matthewcieplak/super-sixteen/graphics/glide-graph.png

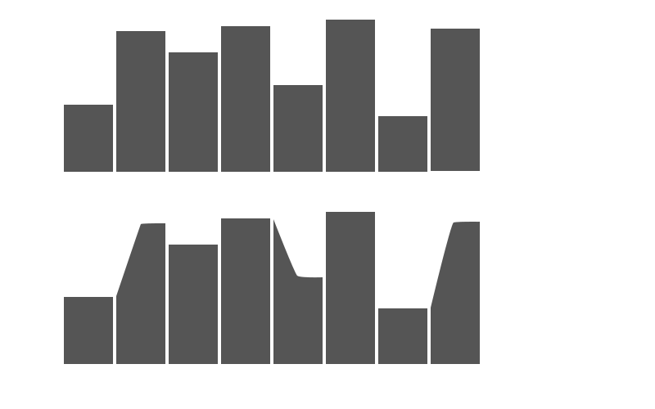
graphics/glide-graph.png
