matthewcieplak/super-sixteen/graphics/calibrate_screen.png

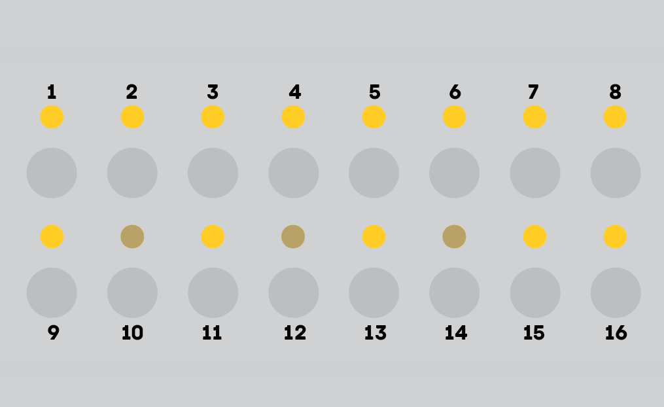
graphics/calibrate_screen.png
