matthewcieplak/super-sixteen/sequencer_app_v2/src/LEDMatrix.cpp

#include <Arduino.h>
#include "Variables.h"
#include "Pinout.h"
#include "Display.h"
#include "Sequencer.h"
#include "LEDMatrix.h"
#include "Buttons.h"
#include "Font.h"

namespace supersixteen{

elapsedMillis multiplex;
elapsedMillis blinker;
bool led_matrix[17];
int step_map[17] = { 3, 2, 1, 0, 0, 1, 2 ,3, 3, 2, 1, 0, 0, 1, 2, 3, 0 }; //rows are wired symmetrically rather than sequentially
int selected_step_led = 0;
const int MILLISECONDS_PER_MULTIPLEX = 1;
const int MILLISECONDS_AFTER_MULTIPLEX = 0;
bool display_active = 1;
byte visible_bar = 0;

uint8_t byte1;
uint8_t byte2;

int row_counter = 0;
int col = 0;
int j;

byte dataToSend;

Display* displayVar3;	
Sequencer* sequencerVar3;

void LedMatrix::init(Display& display, Sequencer& sequencer) {
	pinMode(CS1_PIN, OUTPUT);
	SPI.begin();
	displayVar3 = &display;
	sequencerVar3 = &sequencer;
}

void LedMatrix::updateMatrix(int row) {
	byte1 = (1 << (7-row)); //turn on row driver
	byte2 = 0xF0;
	for (col = 0; col < 4; col++) {
		byte2 +=  (led_matrix[row * 4 + col] << step_map[row * 4 + col]);
	}
	byte1 += ~byte2;
	PORTB = ~_BV(1) & PORTB; //equivalent to digitalWrite(CS1_PIN, LOW);
	SPI.setBitOrder(LSBFIRST); //shift registers like LSB
	displayVar3->updateSevenSegmentDisplay(); //has to happen HERE bc it's part of the shift register 2-byte sequence
	SPI.transfer(byte1); //led matrix  - NOTE: invert this byte if you've wired the LEDs backwards
	PORTB = _BV(1) | PORTB; //equivalent to digitalWrite(CS1_PIN, HIGH);
	displayVar3->nextDigit();
}

void LedMatrix::blankMatrix(int row) {
	displayVar3->blankSevenSegmentDisplay();
	return; //avoid flicker in matrix
	
	byte1 = (1 << (7-row)); //turn on row driver
	byte2 = 0xF0;
	byte1 += ~byte2;
	//PORTB = PORTB & B10111111; //equivalent to 
	digitalWrite(CS1_PIN, LOW);
	SPI.setBitOrder(LSBFIRST); //shift registers like LSB
	displayVar3->blankSevenSegmentDisplay(); //has to happen HERE bc it's part of the shift register 2-byte sequence
	SPI.transfer(~byte1); //led matrix
	//PORTB = PORTB | B01000000; //equivalent to 
	digitalWrite(CS1_PIN, HIGH);
	//displayVar3->nextDigit();
}

void LedMatrix::multiplexLeds() {
	//if (!display_active) {
	  if (multiplex > MILLISECONDS_AFTER_MULTIPLEX) {
	 	multiplex = 0;

		updateMatrix(row_counter);
		//readButtons(row_counter);
		row_counter++;

		if (row_counter == 4) {
			row_counter = 0;
		}

		//updateDisplay();
		display_active = true;
	  }
	// } else if (multiplex > MILLISECONDS_PER_MULTIPLEX) {
	// 	multiplex = 0;
	// 	display_active = false;
	// 	//blankMatrix(row_counter);
	// 	row_counter++;

	// 	if (row_counter == 4) {
	// 		row_counter = 0;
	// 	}
	// }
}

void LedMatrix::blinkStep() {
	//if (blinker < 100) return;
	if (sequencerVar3->getStepOnOff(selected_step_led+visible_bar*16)) {
		if (blinker > (led_matrix[selected_step_led] ? 600 : 100)) { //blink long when active
			blinkLed();
		}
	} else {
		if (blinker > (led_matrix[selected_step_led] ? 100 : 600)) { //blink short when inactive
			blinkLed();
		}
	}
}

void LedMatrix::blinkLed() {
	led_matrix[selected_step_led] = !led_matrix[selected_step_led];
	blinker = 0;
}

void LedMatrix::blinkCurrentStep(){
	int current_step = sequencerVar3->getCurrentStep();
	byte visible_step = current_step % 16;
	if (current_step >= visible_bar*16 && current_step < (visible_bar+1)*16) {
		led_matrix[visible_step] = !led_matrix[visible_step];
	}
}

void LedMatrix::reset(){
	for (int i = 0; i < 16; i++) {
		led_matrix[i] = 0;
	}
}

void LedMatrix::selectStep(int step){
	selected_step_led = step;
}

void LedMatrix::setMatrixFromSequencer(byte bar){
	visible_bar = bar;
	memcpy(led_matrix, sequencerVar3->getStepMatrix()+bar*16, 16); //reset LED matrix to sequence
	selected_step_led = sequencerVar3->getSelectedStep();
	if (selected_step_led < bar*16 || selected_step_led > bar*16+16) {
		selected_step_led = 16; //null step is outside LED matrix
	} else {
		selected_step_led = selected_step_led % 16; //find relative step in current bar
	}
}

void LedMatrix::setMatrix(bool *matrix) {
	memcpy(led_matrix, matrix, 16);
}

void LedMatrix::toggleLed(int led){
	led_matrix[led] = ~led_matrix[led];
}




}
